Michael-A-Sloan/ESP32-Geiger-Counter/src/TEMPLATE_secret_credentials.h

#define _SECRET_CREDENTIALS

// Copy this file to secret_credentials.h and adjust for
// your needs and environment.

// !!! NEVER COMMIT YOUR SECRETS !!!

const char *wifiSsid = "MyWiFi";
const char *wifiPassword = "mypassword";


// ThingsPeak Channel

// set key to NULL or empty string to disable ThingsPeak ingest:
const char *thingspeakApiKey = "MYAPIKEY";


// MQTT Broker

// set host to NULL or empty string to disable MQTT publishing:
const char *mqttHost = "my.mqtt.server";
int mqttPort = 1833;
// set MQTT server's root CA cert to NULL or empty string to disable MQTT TLS/SSL:
const char *mqttTlsServerRootCert = R""""(
-----BEGIN CERTIFICATE-----
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
-----END CERTIFICATE-----
)"""";
const char *mqttUser = "user";
const char *mqttPassword = "mypassword";
const char *mqttTopic = "home/radioactivity";
