Michael-A-Sloan/ESP32-Geiger-Counter/src/credentials.h

#ifndef CREDENTIALS_H_
#define CREDENTIALS_H_

extern const char *wifiSsid;
extern const char *wifiPassword;
extern const char *thingspeakApiKey;

extern const char *mqttHost;
extern int mqttPort;
extern const char *mqttTlsServerRootCert;
extern const char *mqttUser;
extern const char *mqttPassword;
extern const char *mqttTopic;

#endif /* CREDENTIALS_H_ */
